dayalannair/RCWS/matlab_sim/automatedDrivingToolboxSimulations/twoCarLeftRight.pdf

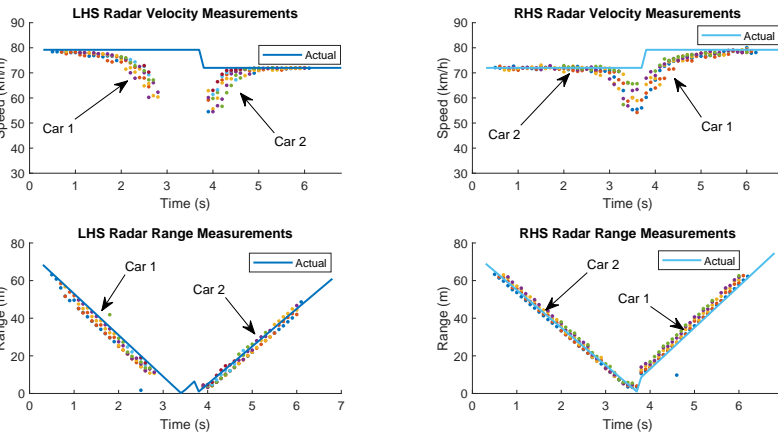
[picture p7: page 1]
Time (s); Speed (km/h); Actual; Range (m); Car 1; Car 2

LHS Radar Velocity Measurements

RHS Radar Velocity Measurements

LHS Radar Range Measurements

RHS Radar Range Measurements
