dayalannair/RCWS/python_dsp/urad_programs/urad_programs/raspberrypi/RCWS_RPi_raw.py

import uRAD_RP_SDK10		# uRAD v1.1 RPi lib
from time import time, sleep

# input parameters
mode = 3					# triangular. Try dual rate mode as well
f0 = 5						# start frequency 24.005 GHz
BW = 240					# sweep 240 MHz
Ns = 100					# 200 samples
Ntar = 1					# 2 target of interest
Rmax = 100					# searching along the full distance range
MTI = 0						# MTI mode enabled: only want information on moving targets
Mth = 1						# MTI threshold. Sets sensitivity with 4 being highest. Vary: find optimal for scenario
Alpha = 10					# signal has to be 10 dB higher than its surrounding. may need tuning
distance_true = False 		# request distance information
velocity_true = False		# request velocity information
SNR_true = False 			# Signal-to-Noise-Ratio information requested
I_true = True 				# In-Phase Component (RAW data) not requested
Q_true = True 				# Quadrature Component (RAW data) not requested
movement_true = False 		# not interested in boolean movement detection

#Switch on Pi uRAD
uRAD_RP_SDK10.turnON()

I = [0] * 2 * Ns
Q = [0] * 2 * Ns
# no return code from SDK 1.0 for RPi
uRAD_RP_SDK10.loadConfiguration(mode, f0, BW, Ns, Ntar, Rmax, MTI, Mth)

I_file = open('I.txt', 'w')
Q_file = open('Q.txt', 'w')

print("Detecting\n")
while True:
	try:
		t = time()
		uRAD_RP_SDK10.detection(0, 0, 0, I, Q, 0)

		I_string = ''
		Q_string = ''

		for index in range(len(I)):
			I_string += '%d ' % I[index]
		for index in range(len(Q)):
			Q_string += '%d ' % Q[index]

		I_file.write(I_string + '%1.3f\n' % t)
		Q_file.write(Q_string + '%1.3f\n' % t)

	except KeyboardInterrupt:
		print("Exiting gracefully\n")
		uRAD_RP_SDK10.turnOFF()
		I_file.close()
		Q_file.close()
		exit()
