dayalannair/RCWS/python_dsp/urad_programs/urad_programs/usb_iq/IQ_save.py

import uRAD_USB_SDK11		# import uRAD libray
import serial
from time import time, sleep

# True if USB, False if UART
usb_communication = True

# input parameters
mode = 3					# sawtooth mode
f0 = 5						# starting at 24.005 GHz
BW = 240					# using all the BW available = 240 MHz
Ns = 200					# 200 samples
Ntar = 1					# Don't apply as only raw data is desired
Rmax = 100					# Don't apply as only raw data is desired
MTI = 2						# MTI mode disable because we want information of static and moving targets
Mth = 1						# Don't apply as only raw data is desired
Alpha = 10					# Don't apply to raw signals
distance_true = False 		# Don't request distance information
velocity_true = False		# Don't request velocity information
SNR_true = False 			# Don't request Signal-to-Noise-Ratio information
I_true = True 				# In-Phase Component (RAW data) requested
Q_true = True 				# Quadrature Component (RAW data) requested
movement_true = False 		# Don't apply as only raw data is desired

# Serial Port configuration
ser = serial.Serial()
if (usb_communication):
	ser.port = '/dev/ttyACM0'
	ser.baudrate = 1e6
else:
	ser.port = '/dev/serial0'
	ser.baudrate = 115200

# Sleep Time (seconds) between iterations
timeSleep = 5e-3

# Other serial parameters
ser.bytesize = serial.EIGHTBITS
ser.parity = serial.PARITY_NONE
ser.stopbits = serial.STOPBITS_ONE
ser.timeout = 1

# Method to correctly turn OFF and close uRAD
def closeProgram():
	# switch OFF uRAD
	return_code = uRAD_USB_SDK11.turnOFF(ser)
	if (return_code != 0):
		exit()

# Open serial port
try:
	ser.open()
except:
	closeProgram()

# switch ON uRAD
return_code = uRAD_USB_SDK11.turnON(ser)
if (return_code != 0):
	closeProgram()

if (not usb_communication):
	sleep(timeSleep)

# loadConfiguration uRAD
return_code = uRAD_USB_SDK11.loadConfiguration(ser, mode, f0, BW, Ns, Ntar, Rmax, MTI, Mth, Alpha, distance_true, velocity_true, SNR_true, I_true, Q_true, movement_true)
if (return_code != 0):
	closeProgram()

if (not usb_communication):
	sleep(timeSleep)

I_file = open('I.txt', 'w')
Q_file = open('Q.txt', 'w')
iterations = 0
t_0 = time()

# infinite detection loop
while True:
	try:
		# target detection request
		return_code, results, raw_results = uRAD_USB_SDK11.detection(ser)
		if (return_code != 0):
			closeProgram()

		# Extract results from outputs
		I = raw_results[0]
		Q = raw_results[1]

		t_i = time()

		I_string = ''
		Q_string = ''
		for index in range(len(I)):
			I_string += '%d ' % I[index]
		for index in range(len(Q)):
			Q_string += '%d ' % Q[index]

		I_file.write(I_string + '%1.3f\n' % t_i)
		Q_file.write(Q_string + '%1.3f\n' % t_i)
		iterations += 1

		if (iterations > 100):
			print('Fs %1.2f Hz' % (iterations/(t_i-t_0)))

		if (not usb_communication):
			sleep(timeSleep)
	except KeyboardInterrupt:
		print("Exiting gracefully\n")
		uRAD_USB_SDK11.turnOFF(ser)
		I_file.close()
		Q_file.close()
		exit()
