dayalannair/RCWS/python_dsp/custom_modules/load_data_lib.py

# Library for loading various types of data in various ways as part of the
# MSc project for dual lane monitoring using radars
# Allows for chaning file and subset length in one place and viewing the results using different scripts

from pathlib import Path
# import numpy as np

# only latest sets here
def load_data():
    # =============================================================================================
    # 3 March 2023
    # =============================================================================================
    # file_path = Path(r"C:\Users\pregg\OneDrive - University of Cape Town\RCWS_DATA\road_data_03_03_2023\iq_data\rhs_iq_12_57_07.txt")
    # file_path = Path(r"C:\Users\pregg\OneDrive - University of Cape Town\RCWS_DATA\road_data_03_03_2023\iq_data\lhs_iq_12_52_01.txt")

    # file_path = Path(r"C:\Users\pregg\OneDrive - University of Cape Town\RCWS_DATA\test_radar\rhs_iq_17_01_40.txt")
    # file_path = Path(r"C:\Users\naird\OneDrive - University of Cape Town\RCWS_DATA\road_data_03_03_2023\iq_data\lhs_iq_12_57_07.txt")
    # file_path = Path(r"C:\Users\naird\OneDrive - University of Cape Town\RCWS_DATA\road_data_03_03_2023\iq_data\rhs_iq_12_57_07.txt")

    # =============================================================================================
    # 30 March 2023
    # =============================================================================================
    # file_path = Path(r"C:\Users\pregg\Desktop\controlled_test_30_03_2023\lhs_iq_12_18_52.txt")
    # file_path = Path(r"C:\Users\pregg\Desktop\controlled_test_30_03_2023\lhs_iq_12_23_14.txt")


    # file_path = Path(r"C:\Users\naird\OneDrive - University of Cape Town\RCWS_DATA\road_data_03_03_2023\iq_data\lhs_iq_12_57_50.txt")

    # file_path = Path(r"C:\Users\naird\OneDrive - University of Cape Town\RCWS_DATA\road_data_03_03_2023\iq_data\lhs_iq_12_52_43.txt")
    # file_path = Path(r"C:\Users\naird\OneDrive - University of Cape Town\RCWS_DATA\road_data_03_03_2023\iq_data\rhs_iq_12_52_43.txt")

    # Yoga - user name is Dayalan Nair not naird. MATLAB does not need the absolute path so it works on both devices
    # file_path = Path(r"C:\Users\Dayalan Nair\OneDrive - University of Cape Town\RCWS_DATA\road_data_03_03_2023\iq_data\lhs_iq_12_57_07.txt")
    # file_path = Path(r"C:\Users\Dayalan Nair\OneDrive - University of Cape Town\RCWS_DATA\road_data_03_03_2023\iq_data\rhs_iq_12_57_07.txt")


    # Controlled test : 23 March 2023
    # file_path = Path(r"C:\Users\naird\OneDrive - University of Cape Town\RCWS_DATA\controlled_test_23_03_2023\rhs_iq_12_45_23.txt")
    # file_path = Path(r"C:\Users\naird\OneDrive - University of Cape Town\RCWS_DATA\controlled_test_23_03_2023\rhs_iq_12_47_44.txt")
    # file_path = Path(r"C:\Users\naird\OneDrive - University of Cape Town\RCWS_DATA\controlled_test_23_03_2023\rhs_iq_12_52_43.txt")

    # Controlled test : 03 April 2023
    # file_path = Path(r"C:\Users\naird\OneDrive - University of Cape Town\RCWS_DATA\controlled_test_03_04_2023\lhs_iq_12_25_03.txt")
    # file_path = Path(r"C:\Users\naird\OneDrive - University of Cape Town\RCWS_DATA\controlled_test_03_04_2023\lhs_iq_12_27_14.txt")
    # file_path = Path(r"C:\Users\naird\OneDrive - University of Cape Town\RCWS_DATA\controlled_test_03_04_2023\lhs_iq_12_29_45.txt")
    # file_path = Path(r"C:\Users\naird\OneDrive - University of Cape Town\RCWS_DATA\controlled_test_03_04_2023\lhs_iq_12_32_47.txt")


    # file_path = Path(r"C:\Users\naird\OneDrive - University of Cape Town\RCWS_DATA\road_data_03_03_2023\iq_data\lhs_iq_12_57_07.txt")
    # file_path = Path(r"C:\Users\naird\OneDrive - University of Cape Town\RCWS_DATA\road_data_03_03_2023\iq_data\rhs_iq_12_57_07.txt")

    file_path = Path(r"C:\Users\naird\OneDrive - University of Cape Town\RCWS_DATA\road_data_03_03_2023\iq_data\lhs_iq_12_52_43.txt")
    # file_path = Path(r"C:\Users\naird\OneDrive - University of Cape Town\RCWS_DATA\road_data_03_03_2023\iq_data\rhs_iq_12_52_43.txt")

    # ------------------------------
    # Controlled tests 23 March 2023
    # ------------------------------
    # 45 km/h
    # subset=range(490,1050) 
    # 60 km/h
    # subset=range(1520,1890)
    # 70 km/h
    subset=range(1700,2060)

    # ------------------------------
    # Controlled tests 03 April 2023
    # ------------------------------
    # 45 km/h
    # subset=range(1030,1390)
    # 60 km/h
    # subset=range(1060,1320)
    # 70 km/h
    subset=range(1100,1360)
    # 60 km/h
    # subset=range(950,1200)

    # Uncontrolled Tests
    # 30-second burst captures (roughly 2740 to 2753)
    subset=range(0,2700)
    

    # sys.path.append('../../../../../OneDrive - University of Cape Town/RCWS_DATA/car_driveby')
    with open(file_path, "r") as raw_IQ:
            # split into sweeps
            # sweeps = raw_IQ.read().split("\n")
            sweeps = raw_IQ.read()
            sweeps = sweeps.split("\n")


    # print(np.shape(sweeps))
    # subset = range(0, np.shape(sweeps)[0]-2)
    return sweeps, subset



def load_data_all_options():

    # file_path = Path(r"C:\Users\naird\OneDrive - University of Cape Town\RCWS_DATA\car_driveby\IQ_tri_20kmh.txt")
    # file_path = Path(r"C:\Users\naird\OneDrive - University of Cape Town\RCWS_DATA\car_driveby\IQ_tri_30kmh.txt")
    # file_path = Path(r"C:\Users\naird\OneDrive - University of Cape Town\RCWS_DATA\car_driveby\IQ_tri_40kmh.txt")
    # file_path = Path(r"C:\Users\naird\OneDrive - University of Cape Town\RCWS_DATA\car_driveby\IQ_tri_50kmh.txt")
    # file_path = Path(r"C:\Users\naird\OneDrive - University of Cape Town\RCWS_DATA\car_driveby\IQ_tri_60kmh.txt")

    # file_path = Path(r"C:\Users\Dayalan Nair\OneDrive - University of Cape Town\RCWS_DATA\car_driveby\IQ_tri_60kmh.txt")

    # file_path = Path(r"C:\Users\naird\OneDrive - University of Cape Town\RCWS_DATA\road_data_03_11_2022\iq_data\lhs_iq_12_18_12.txt")
    # file_path = Path(r"C:\Users\naird\OneDrive - University of Cape Town\RCWS_DATA\road_data_03_11_2022\iq_data\rhs_iq_12_18_12.txt")



    # file_path = Path(r"C:\Users\naird\OneDrive - University of Cape Town\RCWS_DATA\road_data_10_02_2023\iq_data\lhs_iq_14_51_49.txt")
    # file_path = Path(r"C:\Users\naird\OneDrive - University of Cape Town\RCWS_DATA\road_data_10_02_2023\iq_data\rhs_iq_14_51_49.txt")

    # file_path = Path(r"C:\Users\naird\OneDrive - University of Cape Town\RCWS_DATA\road_data_10_02_2023\iq_data\lhs_iq_14_52_54.txt")


    # On laptop Yoga 910

    # file_path = Path(r"C:\Users\Dayalan Nair\OneDrive - University of Cape Town\RCWS_DATA\car_driveby\IQ_tri_60kmh.txt")
    # file_path = Path(r"C:\Users\Dayalan Nair\OneDrive - University of Cape Town\RCWS_DATA\")

    # on Dell XPS 13
    # file_path = Path(r"C:\Users\pregg\Desktop\road_data_31_01_2023\rhs_iq_13_45_20.txt")
    # file_path = Path(r"C:\Users\pregg\OneDrive - University of Cape Town\RCWS_DATA\controlled_test_23_03_2023\rhs_iq_12_43_55.txt")
    # file_path = Path(r"C:\Users\pregg\OneDrive - University of Cape Town\RCWS_DATA\controlled_test_23_03_2023\rhs_iq_12_47_44.txt")
    # file_path = Path(r"C:\Users\pregg\OneDrive - University of Cape Town\RCWS_DATA\controlled_test_23_03_2023\rhs_iq_12_52_43.txt")
    # =============================================================================================
    # 3 March 2023
    # =============================================================================================
    file_path = Path(r"C:\Users\pregg\OneDrive - University of Cape Town\RCWS_DATA\road_data_03_03_2023\iq_data\rhs_iq_12_57_07.txt")
    # file_path = Path(r"C:\Users\pregg\OneDrive - University of Cape Town\RCWS_DATA\road_data_03_03_2023\iq_data\lhs_iq_12_52_01.txt")

    # file_path = Path(r"C:\Users\pregg\OneDrive - University of Cape Town\RCWS_DATA\test_radar\rhs_iq_17_01_40.txt")
    # file_path = Path(r"C:\Users\naird\OneDrive - University of Cape Town\RCWS_DATA\road_data_03_03_2023\iq_data\lhs_iq_12_57_07.txt")
    # file_path = Path(r"C:\Users\naird\OneDrive - University of Cape Town\RCWS_DATA\road_data_03_03_2023\iq_data\rhs_iq_12_57_07.txt")

    # =============================================================================================
    # 30 March 2023
    # =============================================================================================
    # file_path = Path(r"C:\Users\pregg\Desktop\controlled_test_30_03_2023\lhs_iq_12_18_52.txt")
    # file_path = Path(r"C:\Users\pregg\Desktop\controlled_test_30_03_2023\lhs_iq_12_23_14.txt")


    # file_path = Path(r"C:\Users\naird\OneDrive - University of Cape Town\RCWS_DATA\road_data_03_03_2023\iq_data\lhs_iq_12_57_50.txt")

    # file_path = Path(r"C:\Users\naird\OneDrive - University of Cape Town\RCWS_DATA\road_data_03_03_2023\iq_data\lhs_iq_12_52_43.txt")
    # file_path = Path(r"C:\Users\naird\OneDrive - University of Cape Town\RCWS_DATA\road_data_03_03_2023\iq_data\rhs_iq_12_52_43.txt")

    # Yoga - user name is Dayalan Nair not naird. MATLAB does not need the absolute path so it works on both devices
    # file_path = Path(r"C:\Users\Dayalan Nair\OneDrive - University of Cape Town\RCWS_DATA\road_data_03_03_2023\iq_data\lhs_iq_12_57_07.txt")
    # file_path = Path(r"C:\Users\Dayalan Nair\OneDrive - University of Cape Town\RCWS_DATA\road_data_03_03_2023\iq_data\rhs_iq_12_57_07.txt")


    # Controlled test : 23 March 2023
    # file_path = Path(r"C:\Users\naird\OneDrive - University of Cape Town\RCWS_DATA\controlled_test_23_03_2023\rhs_iq_12_45_23.txt")
    # file_path = Path(r"C:\Users\naird\OneDrive - University of Cape Town\RCWS_DATA\controlled_test_23_03_2023\rhs_iq_12_47_44.txt")
    # file_path = Path(r"C:\Users\naird\OneDrive - University of Cape Town\RCWS_DATA\controlled_test_23_03_2023\rhs_iq_12_52_43.txt")

    # Dell XPS
    # file_path = Path(r"C:\Users\pregg\OneDrive - University of Cape Town\RCWS_DATA\controlled_test_23_03_2023\rhs_iq_12_43_55.txt")
    # file_path = Path(r"C:\Users\pregg\OneDrive - University of Cape Town\RCWS_DATA\controlled_test_23_03_2023\rhs_iq_12_47_44.txt")
    # file_path = Path(r"C:\Users\pregg\OneDrive - University of Cape Town\RCWS_DATA\controlled_test_23_03_2023\rhs_iq_12_52_43.txt")
    # subset = range(0, 4000)

    # Controlled test : 03 April 2023
    # file_path = Path(r"C:\Users\naird\OneDrive - University of Cape Town\RCWS_DATA\controlled_test_03_04_2023\lhs_iq_12_25_03.txt")
    # file_path = Path(r"C:\Users\naird\OneDrive - University of Cape Town\RCWS_DATA\controlled_test_03_04_2023\lhs_iq_12_27_14.txt")
    # file_path = Path(r"C:\Users\naird\OneDrive - University of Cape Town\RCWS_DATA\controlled_test_03_04_2023\lhs_iq_12_29_45.txt")
    # file_path = Path(r"C:\Users\naird\OneDrive - University of Cape Town\RCWS_DATA\controlled_test_03_04_2023\lhs_iq_12_32_47.txt")


    # Dell XPS
    # file_path = Path(r"C:\Users\pregg\OneDrive - University of Cape Town\RCWS_DATA\controlled_test_23_03_2023\rhs_iq_12_43_55.txt")
    # file_path = Path(r"C:\Users\pregg\OneDrive - University of Cape Town\RCWS_DATA\controlled_test_23_03_2023\rhs_iq_12_47_44.txt")
    # file_path = Path(r"C:\Users\pregg\OneDrive - University of Cape Town\RCWS_DATA\controlled_test_03_04_2023\lhs_iq_12_32_47.txt")
    # for 30-second burst captures
    # subset = range(0, 2700)

    # # 60kmh subset
    # subset = range(700,1110)
    # # 50 kmh subset
    # subset = range(700,1200)
    # # 40 kmh subset
    # # subset = range(700,1250)
    # subset = range(1350,1900)
    # subset = range(0,1900)

    # Controlled tests 23 March 2023
    # 45 km/h
    # subset=range(0,540) 
    # 60 km/h
    # subset=range(1520,1890)
    # 70 km/h
    # subset=range(1700,2060)

    # subset=range(0,400)
    # subset=range(400,800)
    # subset=range(0,1100)
    # subset=range(0,2700)

    # ------------------------------
    # Controlled tests 23 March 2023
    # ------------------------------
    # 45 km/h
    # subset=range(490,1050) 
    # 60 km/h
    # subset=range(1520,1890)
    # 70 km/h
    # subset=range(1700,2060)

    # ------------------------------
    # Controlled tests 03 April 2023
    # ------------------------------
    # 45 km/h
    # subset=range(1030,1390)
    # 60 km/h
    # subset=range(1060,1320)
    # 70 km/h
    # subset=range(1100,1360)
    # 60 km/h
    # subset=range(950,1200)
    subset=range(0,2700)
    

    # 20km/h subset
    # first car unkown V
    # subset = range(0,550)
    # subset = range(1000,1550)
    # subset = range(0, 3999)

    # sys.path.append('../../../../../OneDrive - University of Cape Town/RCWS_DATA/car_driveby')
    with open(file_path, "r") as raw_IQ:
            # split into sweeps
            # sweeps = raw_IQ.read().split("\n")
            sweeps = raw_IQ.read()
            sweeps = sweeps.split("\n")


    # print(np.shape(sweeps))
    # subset = range(0, np.shape(sweeps)[0]-2)
    return sweeps, subset


def load_dual_data():
    # folder = "road_data_03_11_2022"
    folder = "road_data_05_11_2022"
    # time = "12_18_12"
    time = "11_01_36"
    # file_path_lhs = Path(r"C:\\Users\\naird\\OneDrive - University of Cape Town\\RCWS_DATA\\road_data_05_11_2022\\iq_data\\lhs_iq_11_01_36.txt")
    # file_path_rhs = Path(r"C:\\Users\\naird\\OneDrive - University of Cape Town\\RCWS_DATA\\road_data_05_11_2022\\iq_data\\rhs_iq_11_01_36.txt")

    # subset = range(0, 4000)
    subset = range(500, 2000)
    # 50 kmh subset - same
    # 40 kmh subset
    # subset = range(700,1100)
    # 20km/h subset
    # subset = range(1,1500)
    file_path_lhs = Path(r"C:\Users\pregg\Desktop\road_data_31_01_2023\lhs_iq_13_45_20.txt")
    file_path_rhs = Path(r"C:\Users\pregg\Desktop\road_data_31_01_2023\rhs_iq_13_45_20.txt")
    # sys.path.append('../../../../../OneDrive - University of Cape Town/RCWS_DATA/car_driveby')
    
    with open(file_path_lhs, "r") as raw_IQ_lhs:
        lhs = raw_IQ_lhs.read().split("\n")

    with open(file_path_rhs, "r") as raw_IQ_rhs:
        rhs = raw_IQ_rhs.read().split("\n")
    return lhs, rhs, subset


def load_proc_data():
    
    # file_path_lhs = Path(r"lhs_speed_results.txt")
    # file_path_rhs = Path(r"rhs_speed_results.txt")

    # subset = range(0, 4000)
    # subset = range(0, 350)
    # 50 kmh subset - same
    # 40 kmh subset
    # subset = range(700,1100)
    # 20km/h subset
    # subset = range(1,1500)

    # sys.path.append('../../../../../OneDrive - University of Cape Town/RCWS_DATA/car_driveby')
     # =============================================================================================
    # 3 March 2023
    # =============================================================================================

    # file_path = Path(r"C:\Users\naird\OneDrive - University of Cape Town\RCWS_DATA\road_data_03_03_2023\iq_data\lhs_iq_12_57_07.txt")
    # file_path = Path(r"C:\Users\naird\OneDrive - University of Cape Town\RCWS_DATA\road_data_03_03_2023\iq_data\rhs_iq_12_57_07.txt")

    # file_path = Path(r"C:\Users\naird\OneDrive - University of Cape Town\RCWS_DATA\road_data_03_03_2023\iq_data\lhs_iq_12_57_50.txt")

    # file_path = Path(r"C:\Users\naird\OneDrive - University of Cape Town\RCWS_DATA\road_data_03_03_2023\iq_data\lhs_iq_12_52_43.txt")
    # file_path = Path(r"C:\Users\naird\OneDrive - University of Cape Town\RCWS_DATA\road_data_03_03_2023\iq_data\rhs_iq_12_52_43.txt")

    # Yoga - user name is Dayalan Nair not naird. MATLAB does not need the absolute path so it works on both devices
    file_path_lhs = Path(r"C:\Users\naird\OneDrive - University of Cape Town\RCWS_DATA\road_data_03_03_2023\rt_proc_data\2thd_lhs_speed_results_12_54_30.txt")
    file_path_rhs = Path(r"C:\Users\naird\OneDrive - University of Cape Town\RCWS_DATA\road_data_03_03_2023\rt_proc_data\2thd_rhs_speed_results_12_54_30.txt")
    # file_path = Path(r"C:\Users\Dayalan Nair\OneDrive - University of Cape Town\RCWS_DATA\road_data_03_03_2023\iq_data\rhs_iq_12_57_07.txt")

    # file_path_lhs = Path(r"C:\Users\naird\OneDrive - University of Cape Town\RCWS_DATA\road_data_03_03_2023\rt_proc_data\2thd_lhs_speed_results_12_59_14.txt")
    # file_path_rhs = Path(r"C:\Users\naird\OneDrive - University of Cape Town\RCWS_DATA\road_data_03_03_2023\rt_proc_data\2thd_rhs_speed_results_12_59_14.txt")
    
    # file_path_lhs = Path(r"C:\Users\naird\OneDrive - University of Cape Town\RCWS_DATA\road_data_03_03_2023\rt_proc_data\2thd_lhs_speed_results_12_58_38.txt")
    # file_path_rhs = Path(r"C:\Users\naird\OneDrive - University of Cape Town\RCWS_DATA\road_data_03_03_2023\rt_proc_data\2thd_rhs_speed_results_12_58_38.txt")

    # file_path_lhs = Path(r"C:\Users\naird\OneDrive - University of Cape Town\RCWS_DATA\road_data_03_03_2023\rt_proc_data\2thd_lhs_speed_results_12_59_14.txt")
    # file_path_rhs = Path(r"C:\Users\naird\OneDrive - University of Cape Town\RCWS_DATA\road_data_03_03_2023\rt_proc_data\2thd_rhs_speed_results_12_59_14.txt")
    
    
    # 5 April 2023 - final test
    # _12_09_39
    # _12_13_03
    # _12_13_42
    # _12_14_57
    file_path_lhs = Path(r"C:\Users\naird\OneDrive - University of Cape Town\RCWS_DATA\road_data_11_04_2023\2thd_lhs_speed_results_12_09_39.txt")
    file_path_rhs = Path(r"C:\Users\naird\OneDrive - University of Cape Town\RCWS_DATA\road_data_11_04_2023\2thd_rhs_speed_results_12_09_39.txt")


    with open(file_path_lhs, "r") as raw_IQ_lhs:
        lhsSpd = raw_IQ_lhs.read().split("\n")

    with open(file_path_rhs, "r") as raw_IQ_rhs:
        rhsSpd = raw_IQ_rhs.read().split("\n")

    file_path_lhs = Path(r"C:\Users\naird\OneDrive - University of Cape Town\RCWS_DATA\road_data_11_04_2023\2thd_lhs_range_results_12_09_39.txt")
    file_path_rhs = Path(r"C:\Users\naird\OneDrive - University of Cape Town\RCWS_DATA\road_data_11_04_2023\2thd_rhs_range_results_12_09_39.txt")


    with open(file_path_lhs, "r") as raw_IQ_lhs:
        lhsRng = raw_IQ_lhs.read().split("\n")

    with open(file_path_rhs, "r") as raw_IQ_rhs:
        rhsRng = raw_IQ_rhs.read().split("\n")

    file_path_lhs = Path(r"C:\Users\naird\OneDrive - University of Cape Town\RCWS_DATA\road_data_11_04_2023\2thd_lhs_safety_results_12_09_39.txt")
    file_path_rhs = Path(r"C:\Users\naird\OneDrive - University of Cape Town\RCWS_DATA\road_data_11_04_2023\2thd_rhs_safety_results_12_09_39.txt")


    with open(file_path_lhs, "r") as raw_IQ_lhs:
        lhsSft = raw_IQ_lhs.read().split("\n")

    with open(file_path_rhs, "r") as raw_IQ_rhs:
        rhsSft = raw_IQ_rhs.read().split("\n")

    len_subset = len(rhsSft)
    return lhsSpd, rhsSpd, lhsRng, rhsRng, lhsSft, rhsSft, len_subset


def load_video():
    lhs_vid_name = Path(r"C:\Users\naird\OneDrive - University of Cape Town\RCWS_DATA\road_data_03_11_2022\iq_vid\lhs_vid_12_18_12.avi")
    rhs_vid_name = Path(r"C:\Users\naird\OneDrive - University of Cape Town\RCWS_DATA\road_data_03_11_2022\iq_vid\rhs_vid_12_18_12.avi")

    return lhs_vid_name, rhs_vid_name
